BigCorvus/LORA-QWERTY-Communicator/Q10 Lora Communicator/Arduino/LORA_Messenger/appBLEsensors.ino

void appBLEsensors(){
  //start sequence
  //display Stuff, initialize....
  display.clearDisplay();
  display.setFont(&FreeSans18pt7b);

  //display.setTextSize(3); //standard font is 5x8, so scale it by 3 ->15x24
  display.setCursor(25, 30);
  display.setTextColor(BLACK);
  display.println("BLE Sensors");
  display.refresh();
  while (insideSubMenue) { //the back button terminates the loop
    readKeyboard(); //navigate with "WASD"
    readWASD();
    //loop of the APP
    delay(100); //get some sleep else the app hangs!
   }
   insideBLEsensors=false;
  displayMenue(menueIndex);
}
